maxr777/weather-station/main/led.h

#ifndef LED_H
#define LED_H

#include "driver/gpio.h"

#define WHITE_LED_GPIO 13
#define BLUE_LED_GPIO  27
#define RED_LED_GPIO   33
#define GREEN_LED_GPIO 32

typedef enum {
	WHITE,
	BLUE,
	RED,
	GREEN,
	COLOR_COUNT,
} LEDColor;

static inline int GetLEDGPIO(const LEDColor c) {
	switch (c) {
	case WHITE:
		return WHITE_LED_GPIO;
	case BLUE:
		return BLUE_LED_GPIO;
	case RED:
		return RED_LED_GPIO;
	case GREEN:
		return GREEN_LED_GPIO;
	default:
		return -1;
	}
}

// TODO: error check
static inline void EnableLED(const LEDColor c) {
	int gpio = GetLEDGPIO(c);
	if (gpio != -1)
		gpio_set_level(gpio, 1);
}

static inline void DisableLED(const LEDColor c) {
	int gpio = GetLEDGPIO(c);
	if (gpio != -1)
		gpio_set_level(gpio, 0);
}

#endif
